patdie421/no.slot.clock-neo/IMG_3980.jpeg

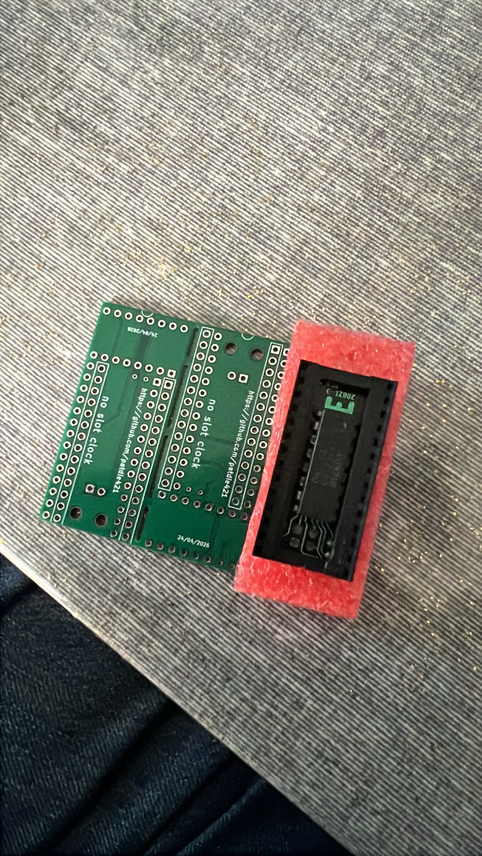
IMG_3980.jpeg
